heresiarch/Firefly/firefly2/wave.h

/*
    created with Fireflies WaveEditor written by H. Reddmann
    HaReddmann at t-online dot de
*/

#ifndef WAVE_H
#define WAVE_H

#include <inttypes.h>
#include <avr/pgmspace.h>

#define WAVE_COUNT  32

typedef struct {
    const prog_uint8_t* start;
    const prog_uint8_t* stop;
    const uint16_t energy;
} wave_data_t;

#if 0
#define WVFACTOR 1
const prog_uint8_t wave[827] PROGMEM = {
	0x16,0x2F,0x49,0x64,0x7F,0x99,0xB1,0xC8,0xDB,0xEA,0xF5,0xFA,0xF9,0xF2,0xE6,0xD5,
	0xC1,0xAA,0x91,0x78,0x5F,0x46,0x30,0x1C,0x0D,0x03,0x02,0x07,0x0E,0x14,0x19,0x1D,
	0x1F,0x1F,0x1F,0x1F,0x1F,0x1F,0x1F,0x1F,0x1F,0x1E,0x1E,0x1E,0x1E,0x1E,0x1E,0x1E,
	0x1E,0x1E,0x1E,0x1E,0x1E,0x1E,0x1E,0x1E,0x1E,0x1E,0x1E,0x1E,0x1E,0x1E,0x1E,0x1D,
	0x1D,0x1D,0x1D,0x1D,0x1D,0x1D,0x1D,0x1D,0x1D,0x1D,0x1D,0x1D,0x1E,0x1E,0x1D,0x1D,
	0x1D,0x1D,0x1D,0x1D,0x1E,0x1E,0x1E,0x1E,0x1E,0x1E,0x1D,0x1B,0x19,0x16,0x12,0x0E,
	0x09,0x05,0x01,0x06,0x0C,0x14,0x1B,0x23,0x2C,0x34,0x3C,0x44,0x4C,0x53,0x59,0x5D,
	0x5D,0x5B,0x56,0x51,0x4B,0x45,0x40,0x3D,0x3D,0x40,0x48,0x53,0x61,0x70,0x80,0x90,
	0xA0,0xAF,0xBB,0xC6,0xCD,0xD1,0xD0,0xCB,0xC3,0xB8,0xAB,0x9C,0x8B,0x7A,0x67,0x55,
	0x43,0x31,0x20,0x12,0x09,0x03,0x01,0x03,0x07,0x0A,0x0D,0x0E,0x0E,0x0D,0x0C,0x0B,
	0x0B,0x0B,0x0B,0x0B,0x0C,0x0D,0x0E,0x0F,0x11,0x13,0x14,0x16,0x17,0x19,0x1A,0x1C,
	0x1D,0x1F,0x20,0x22,0x23,0x24,0x25,0x25,0x26,0x25,0x25,0x25,0x24,0x24,0x23,0x23,
	0x23,0x23,0x23,0x23,0x23,0x23,0x23,0x23,0x23,0x23,0x23,0x24,0x24,0x24,0x24,0x24,
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
	{&wave[ 435 * WVFACTOR], &wave[ 461 * WVFACTOR],  559},
	{&wave[ 435 * WVFACTOR], &wave[ 534 * WVFACTOR], 1712},
	{&wave[ 435 * WVFACTOR], &wave[ 693 * WVFACTOR], 1745},
	{&wave[ 461 * WVFACTOR], &wave[ 534 * WVFACTOR], 1618},
	{&wave[ 461 * WVFACTOR], &wave[ 693 * WVFACTOR], 1653},
	{&wave[ 534 * WVFACTOR], &wave[ 693 * WVFACTOR],  338},
	{&wave[ 534 * WVFACTOR], &wave[ 827 * WVFACTOR],  987},
	{&wave[ 693 * WVFACTOR], &wave[ 827 * WVFACTOR],  927}
};

#endif
